sindisv/BachelorThesisHSRW/Training Sessions CSV and XLSX Files/plots_complete/1a_all_devices.png

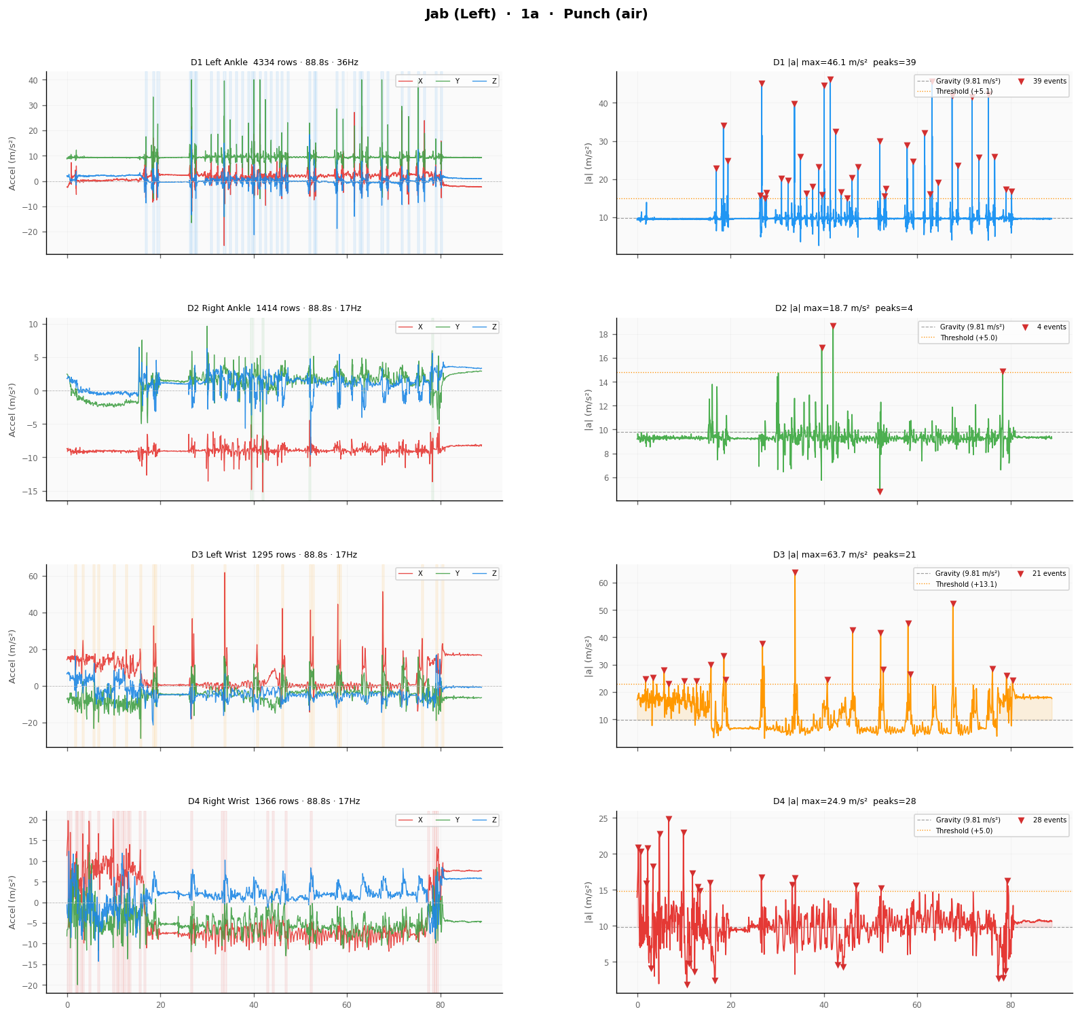
Training Sessions CSV and XLSX Files/plots_complete/1a_all_devices.png
