sindisv/BachelorThesisHSRW/Training Sessions CSV and XLSX Files/plots_complete/1d_all_devices.png

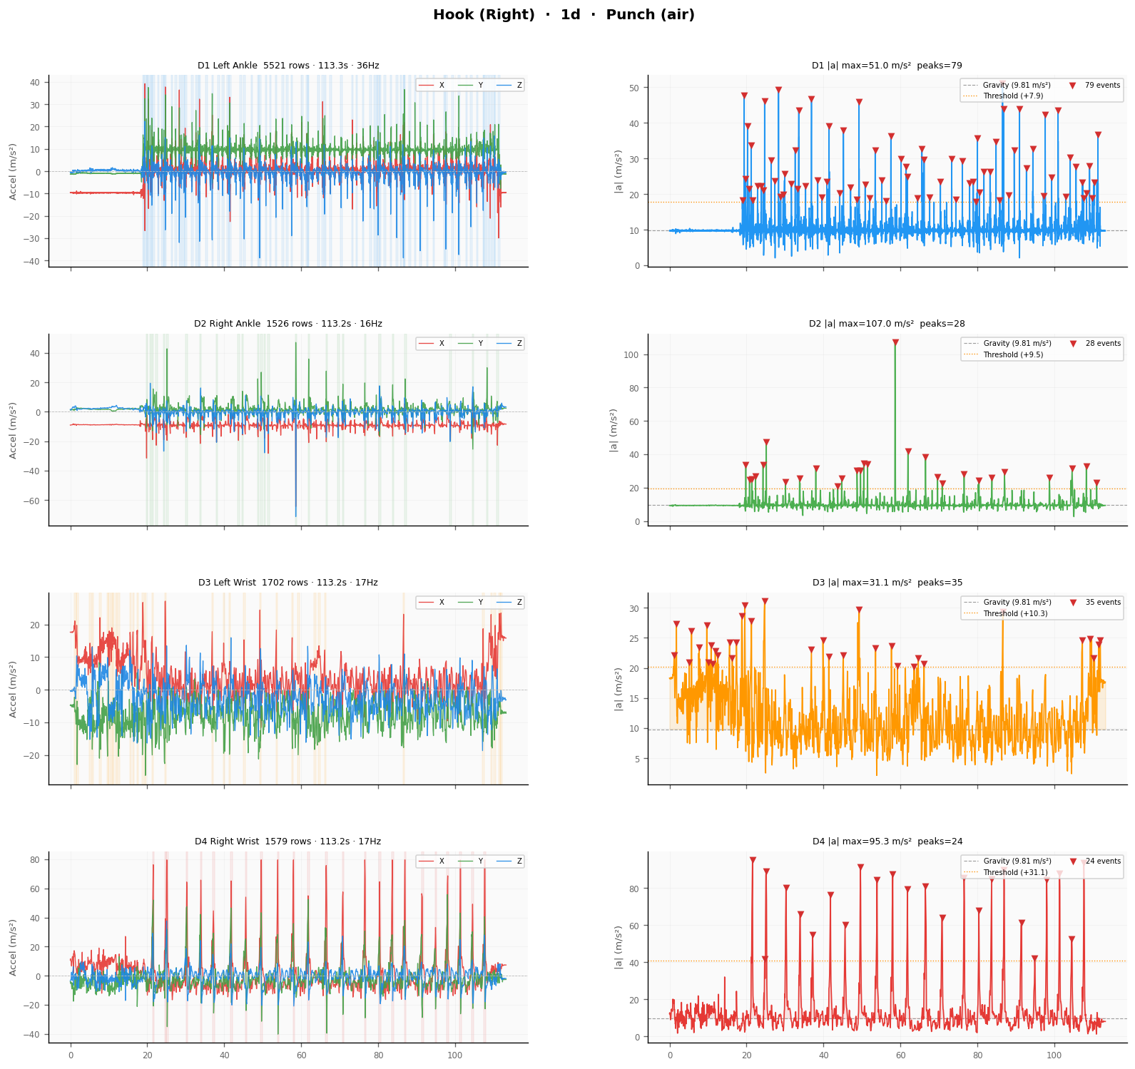
Training Sessions CSV and XLSX Files/plots_complete/1d_all_devices.png
