sindisv/BachelorThesisHSRW/Training Sessions CSV and XLSX Files/plots_complete/compare_air_vs_bag.png

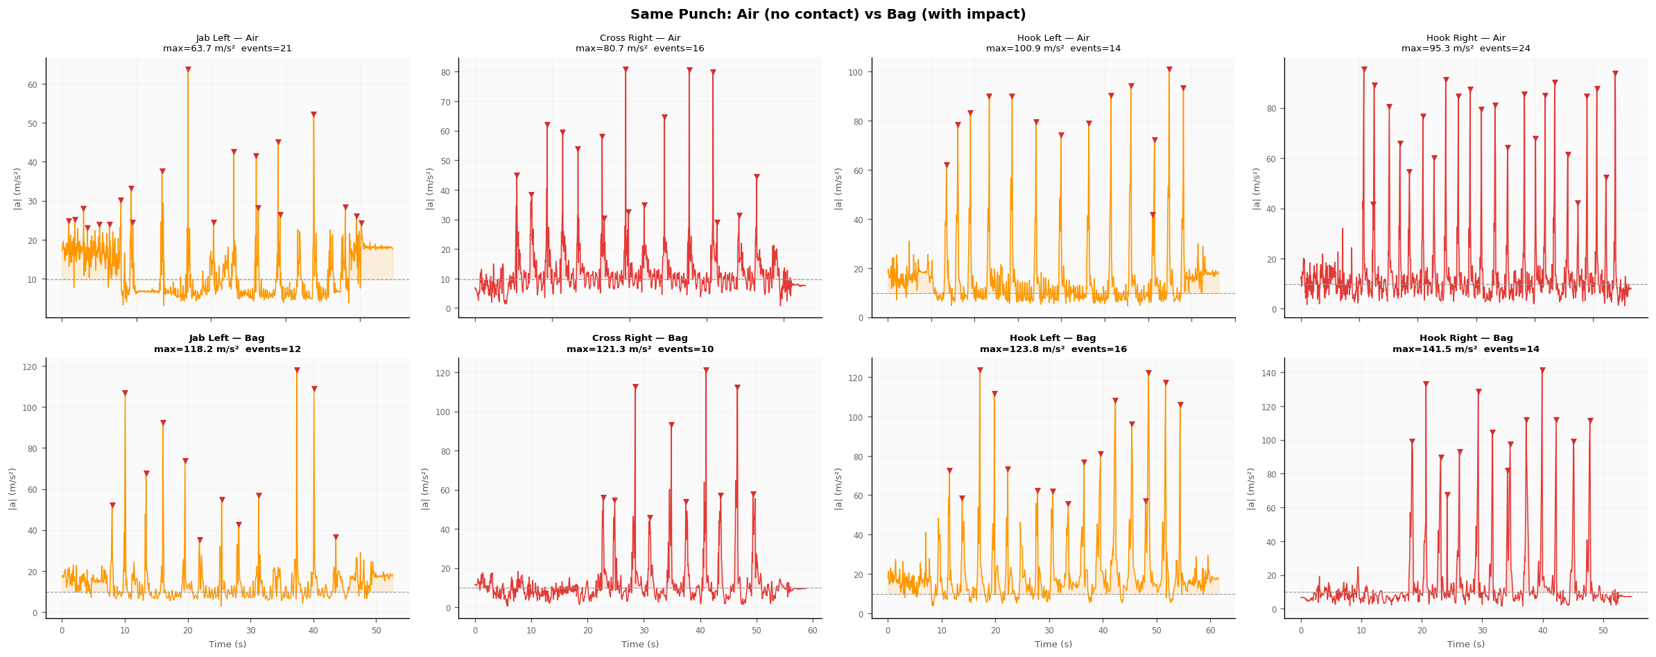
Training Sessions CSV and XLSX Files/plots_complete/compare_air_vs_bag.png
