sindisv/BachelorThesisHSRW/Training Sessions CSV and XLSX Files/plots_complete/compare_High_Kick_LR.png

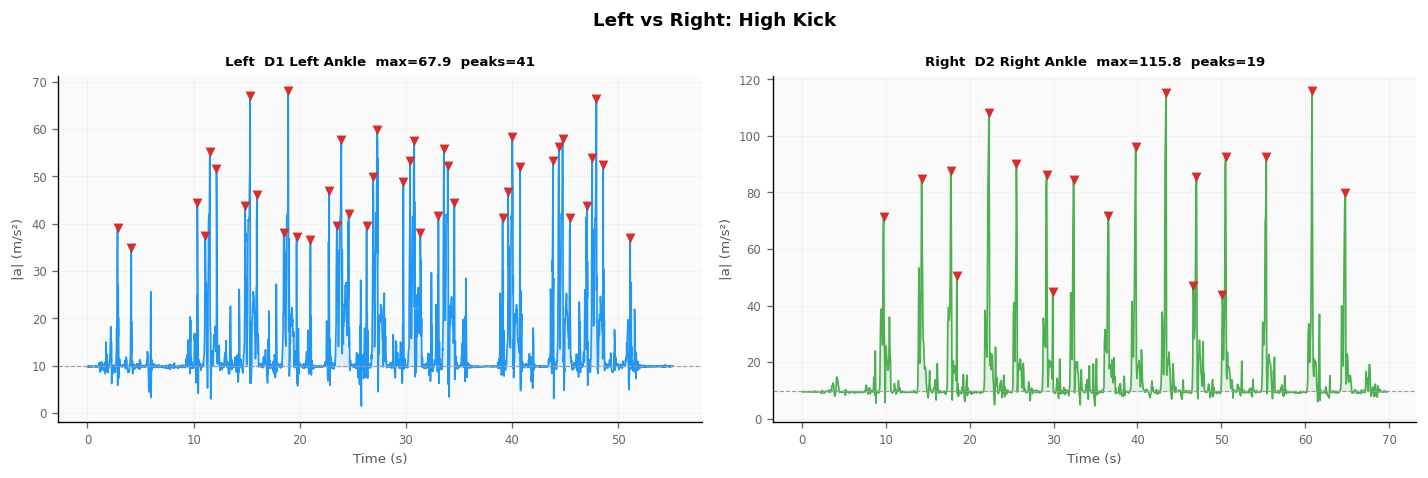
Training Sessions CSV and XLSX Files/plots_complete/compare_High_Kick_LR.png
