sindisv/BachelorThesisHSRW/Training Sessions CSV and XLSX Files/plots_complete/compare_Low_Kick_LR.png

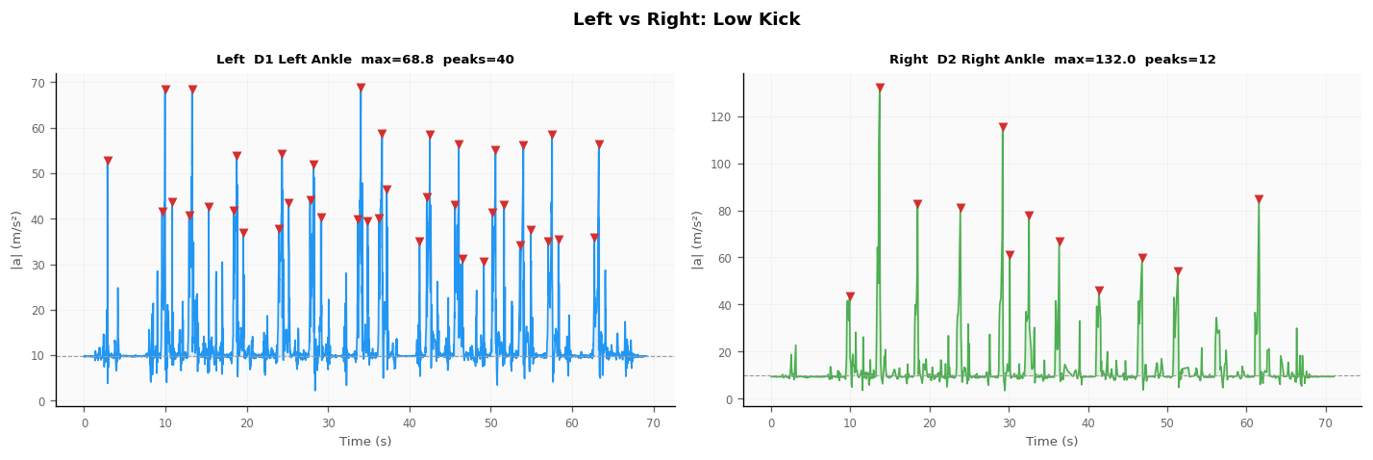
Training Sessions CSV and XLSX Files/plots_complete/compare_Low_Kick_LR.png
