sindisv/BachelorThesisHSRW/Training Sessions CSV and XLSX Files/Session 2 (Specific Motions)/session2plots/Boxinghookdevice3_analysis.png

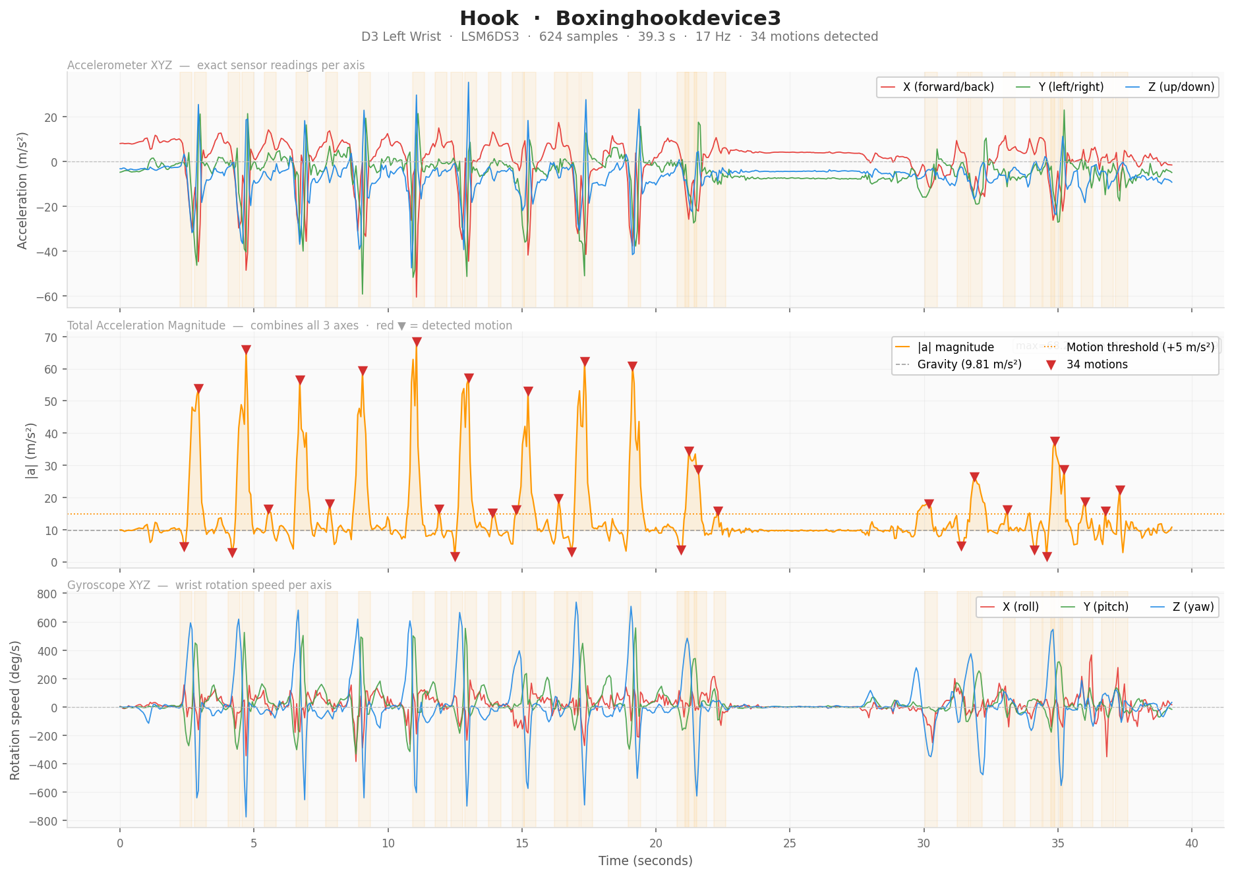
Training Sessions CSV and XLSX Files/Session 2 (Specific Motions)/session2plots/Boxinghookdevice3_analysis.png
