sindisv/BachelorThesisHSRW/Training Sessions CSV and XLSX Files/Session 2 (Specific Motions)/session2plots/comparisonuppercutdevice1device3.png

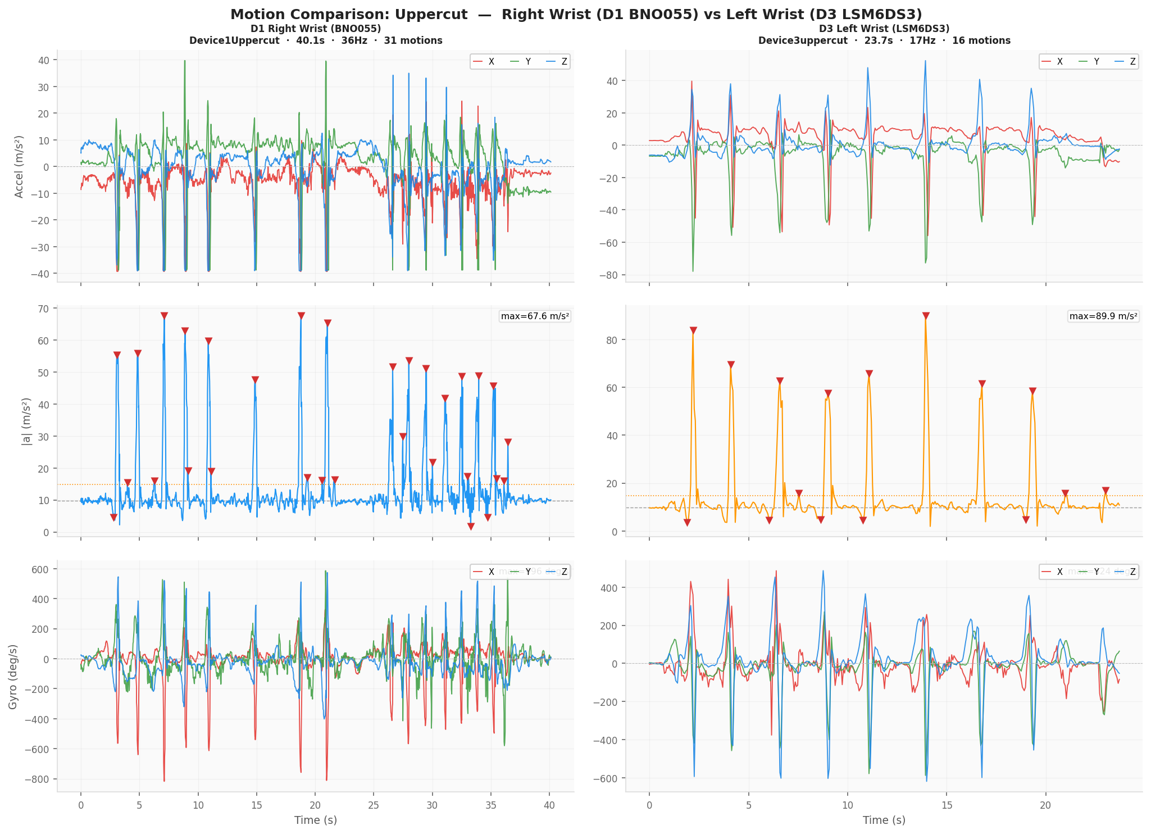
Training Sessions CSV and XLSX Files/Session 2 (Specific Motions)/session2plots/comparisonuppercutdevice1device3.png
