sindisv/BachelorThesisHSRW/CAD Files Fusion360/3D Files Fusion360/Unit 1 Parts/XIAO-nRF52840 v15 v1.step

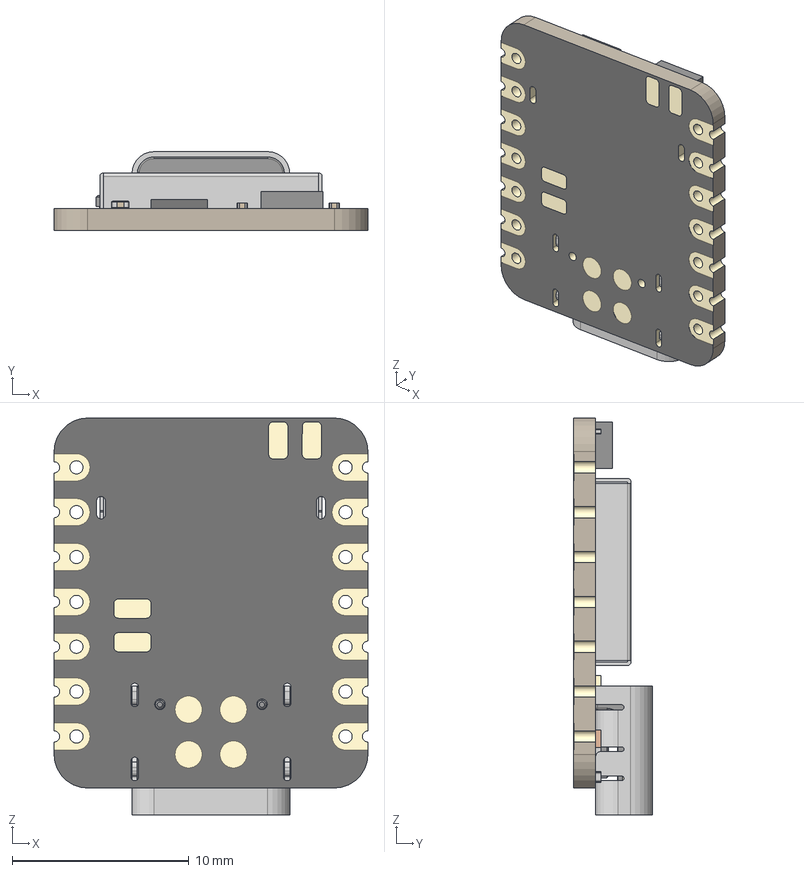
[picture p44: CAD file, 2026-06-12]
CAD Files Fusion360/3D Files Fusion360/Unit 1 Parts/XIAO-nRF52840 v15 v1.step
17.8 x 4.46 x 22.5 mm
BOSS-EXTRUDE14_8_
BOSS-EXTRUDE7_4_
BOSS-EXTRUDE7_3_
BOSS-EXTRUDE14_4_
BOSS-EXTRUDE14_2_
BOSS-EXTRUDE14_11_
BOSS-EXTRUDE7_7_
BOSS-EXTRUDE14_9_
BOSS-EXTRUDE14_3_
BOSS-EXTRUDE14_7_
MIRROR2
BOSS-EXTRUDE14_5_
BOSS-EXTRUDE14_12_
BOSS-EXTRUDE7_8_
BOSS-EXTRUDE7_1_
BOSS-EXTRUDE14_10_
BOSS-EXTRUDE7_9_
BOSS-EXTRUDE14_6_
BOSS-EXTRUDE14_1_
BOSS-EXTRUDE7_6_
BOSS-EXTRUDE7_2_
CUT-EXTRUDE5
BOSS-EXTRUDE7_5_
Shield
Pins
CAP x 2
ANT1
Silkscreen
CAP 3
LED
USR
MSM261D3526H1CPM
