sindisv/BachelorThesisHSRW/CAD Files Fusion360/3D Files Fusion360/Unit 2 Parts/Enclosure Lid Unit 2.step

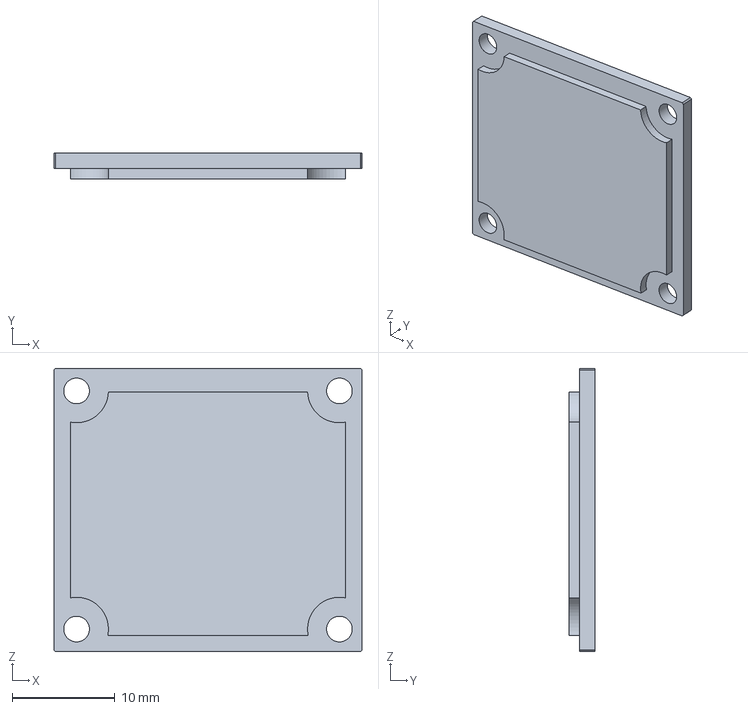
[picture p45: CAD file, 2026-06-12]
CAD Files Fusion360/3D Files Fusion360/Unit 2 Parts/Enclosure Lid Unit 2.step
30.0 x 2.50 x 27.6 mm
