sindisv/BachelorThesisHSRW/CAD Files Fusion360/3D Files Fusion360/Unit 2 Parts/Enclosure Unit 2.step

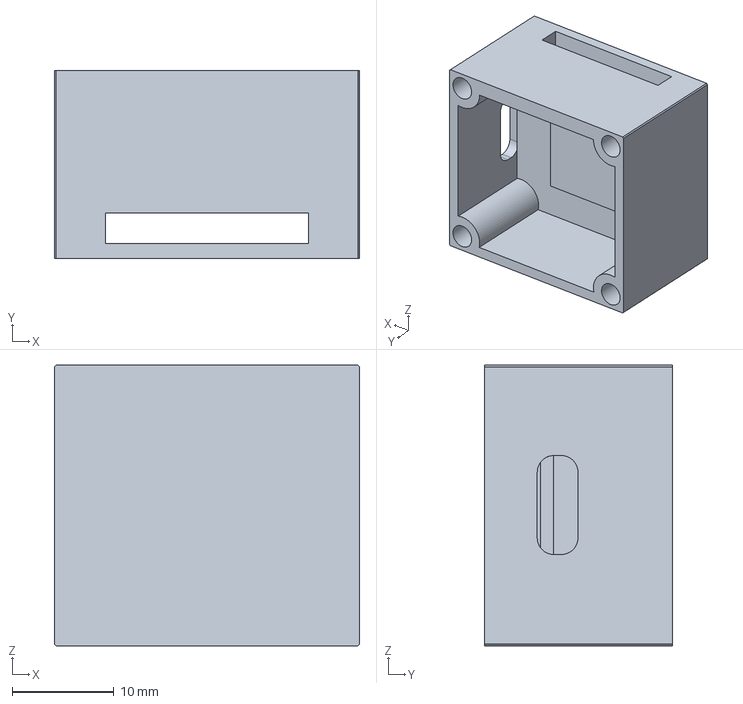
[picture p46: CAD file, 2026-06-12]
CAD Files Fusion360/3D Files Fusion360/Unit 2 Parts/Enclosure Unit 2.step
30.0 x 18.5 x 27.6 mm
