sindisv/BachelorThesisHSRW/CAD Files Fusion360/3D Files Fusion360/Unit 1 Parts/Adafruit_BNO055_AP214.step

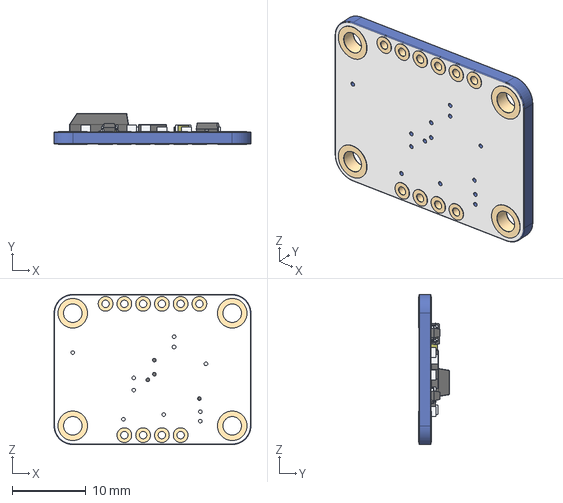
[picture p47: CAD file, 2026-06-12]
CAD Files Fusion360/3D Files Fusion360/Unit 1 Parts/Adafruit_BNO055_AP214.step
26.7 x 4.20 x 20.3 mm
