sindisv/BachelorThesisHSRW/CAD Files Fusion360/3D Files Fusion360/Unit 3&4 Parts/Enclosure Lid Unit 3,4.step

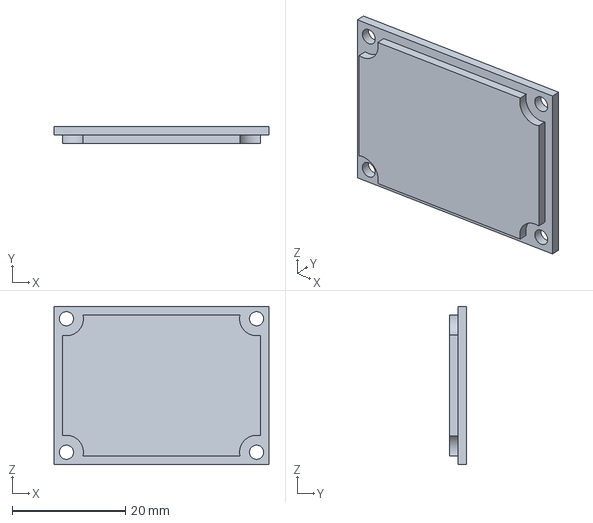
[picture p48: CAD file, 2026-06-12]
CAD Files Fusion360/3D Files Fusion360/Unit 3&4 Parts/Enclosure Lid Unit 3,4.step
38.0 x 3.00 x 28.0 mm
