sindisv/BachelorThesisHSRW/CAD Files Fusion360/3D Files Fusion360/Unit 1 Parts/Enclosure Lid Unit 1.step

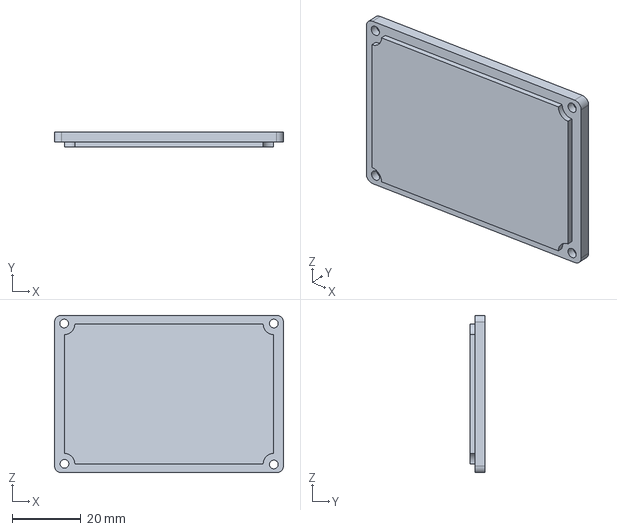
[picture p49: CAD file, 2026-06-12]
CAD Files Fusion360/3D Files Fusion360/Unit 1 Parts/Enclosure Lid Unit 1.step
66.6 x 4.50 x 45.8 mm
