sindisv/BachelorThesisHSRW/Electrical Schematics KiCad/Circuit Device 1.kicad_sch

## KiCad design Electrical Schematics KiCad/Circuit Device 1.kicad_sch (2026-06-12)

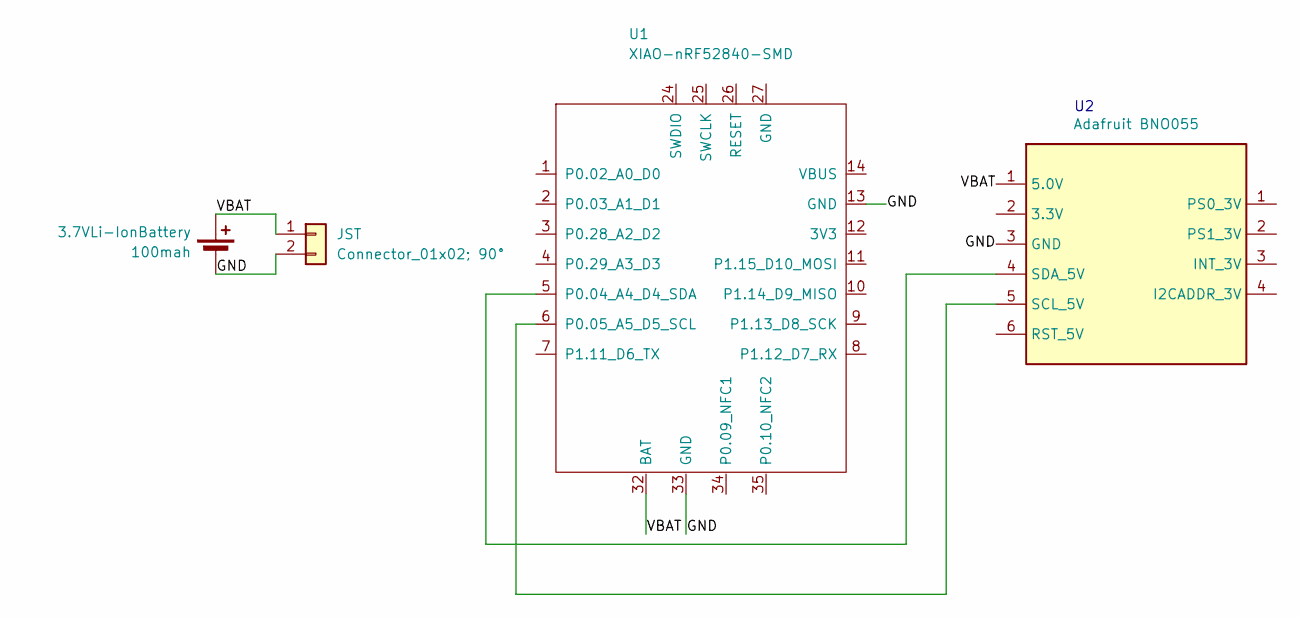
[picture p56: schematic Circuit Device 1.kicad_sch]

Parts:
3.7VLi-IonBattery: 100mah
JST: Connector_01x02; 90°
U1: XIAO-nRF52840-SMD

Connections:
GND: 3.7VLi-IonBattery.2 (-), JST.2, U1.3 (GND), U1.13 (GND), U1.33 (GND)
unnamed: U1.4 (SDA_5V), U1.5 (SCL_5V)
unnamed: U1.5 (SCL_5V), U1.6 (RST_5V)
VBAT: 3.7VLi-IonBattery.1 (+), JST.1, U1.1 (5.0V), U1.32 (BAT)
