sindisv/BachelorThesisHSRW/Electrical Schematics KiCad/Circuit Device 2.kicad_sch

## KiCad design Electrical Schematics KiCad/Circuit Device 2.kicad_sch (2026-06-12)

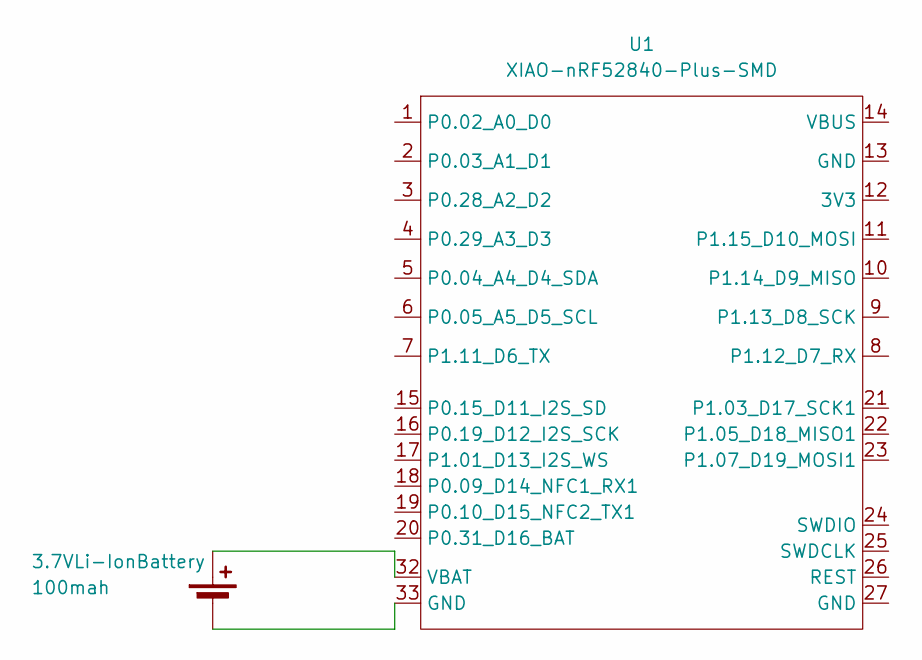
[picture p57: schematic Circuit Device 2.kicad_sch]

Parts:
3.7VLi-IonBattery: 100mah
U1: XIAO-nRF52840-Plus-SMD

Connections:
unnamed: 3.7VLi-IonBattery.1 (+), U1.32 (VBAT)
unnamed: 3.7VLi-IonBattery.2 (-), U1.33 (GND)
