sindisv/BachelorThesisHSRW/Electrical Schematics KiCad/Circuit Device 3 and Device 4.kicad_sch

## KiCad design Electrical Schematics KiCad/Circuit Device 3 and Device 4.kicad_sch (2026-06-12)

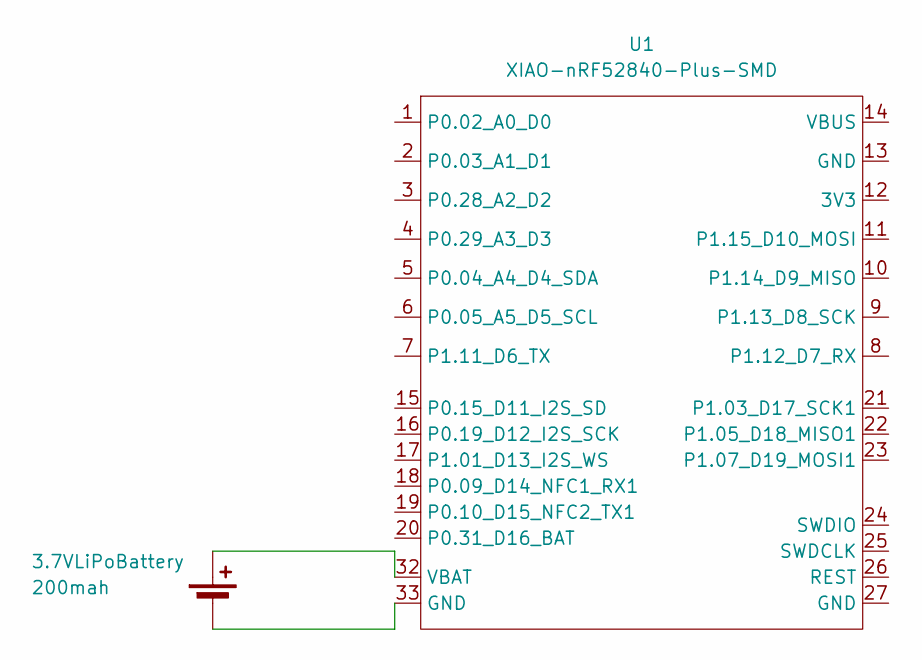
[picture p58: schematic Circuit Device 3 and Device 4.kicad_sch]

Parts:
3.7VLiPoBattery: 200mah
U1: XIAO-nRF52840-Plus-SMD

Connections:
unnamed: 3.7VLiPoBattery.1 (+), U1.32 (VBAT)
unnamed: 3.7VLiPoBattery.2 (-), U1.33 (GND)
